OjasKulkarni33/-MED-30.105-Nerf-Gun-Project/Step Files/RotatingDrumSubAssy/Follower.step

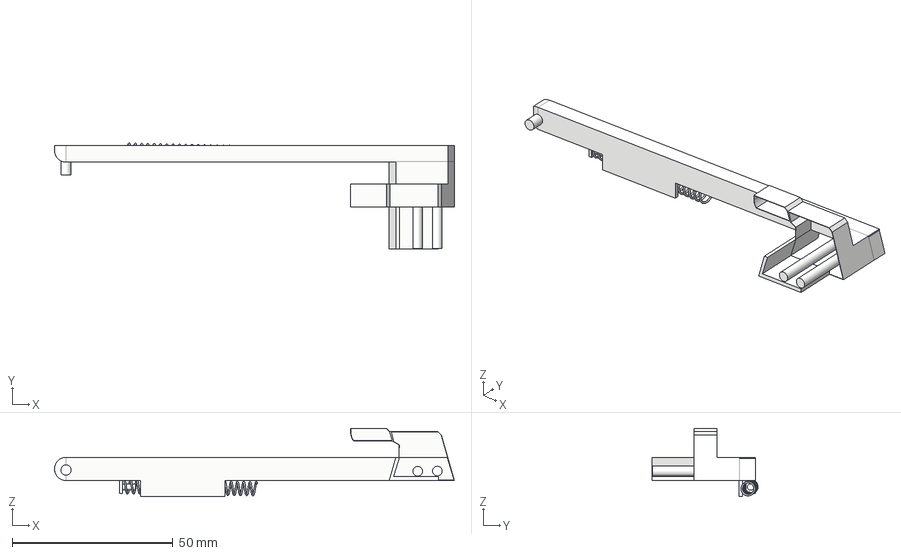
[picture p45: CAD file, 2026-08-20]
Step Files/RotatingDrumSubAssy/Follower.step
124.2 x 33.0 x 21.2 mm
Handle
