OjasKulkarni33/-MED-30.105-Nerf-Gun-Project/Step Files/PrimingSubAssy/Trigger.step

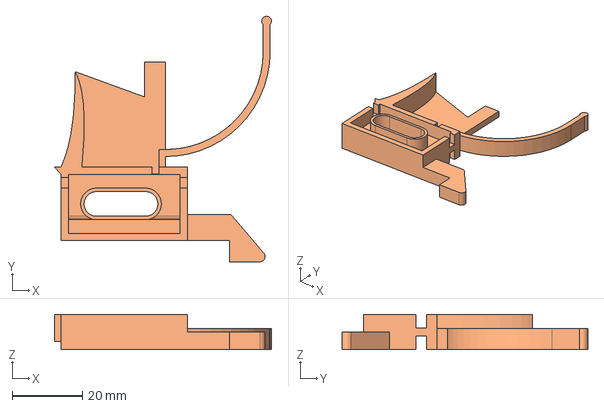
[picture p46: CAD file, 2026-08-20]
Step Files/PrimingSubAssy/Trigger.step
61.9 x 70.0 x 10.0 mm
