OjasKulkarni33/-MED-30.105-Nerf-Gun-Project/Step Files/RotatingDrumSubAssy/ConnectionPiece.step

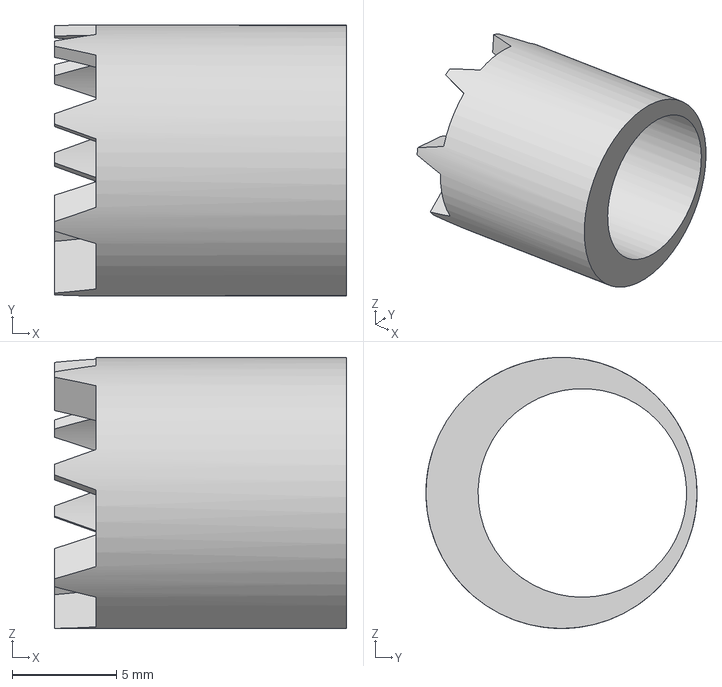
[picture p47: CAD file, 2026-08-20]
Step Files/RotatingDrumSubAssy/ConnectionPiece.step
14.0 x 13.0 x 13.0 mm
