OjasKulkarni33/-MED-30.105-Nerf-Gun-Project/Step Files/CoverFrameSubAssy/CoverFrame_[Right].png

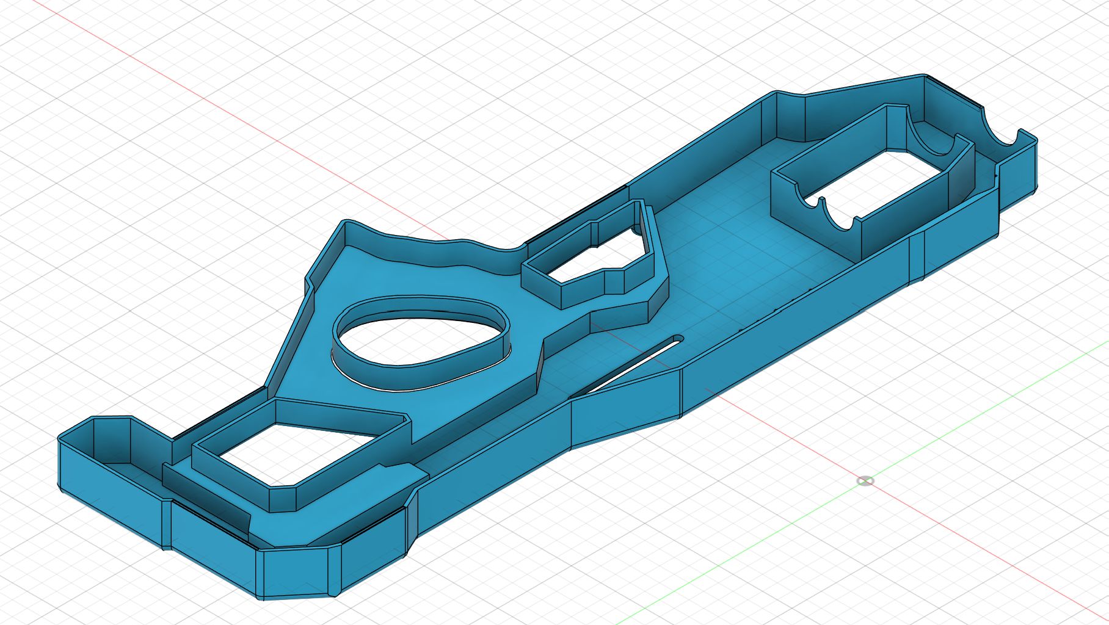
Step Files/CoverFrameSubAssy/CoverFrame_[Right].png
