OjasKulkarni33/-MED-30.105-Nerf-Gun-Project/Step Files/CoverFrameSubAssy/CoverFrameAssembly.png

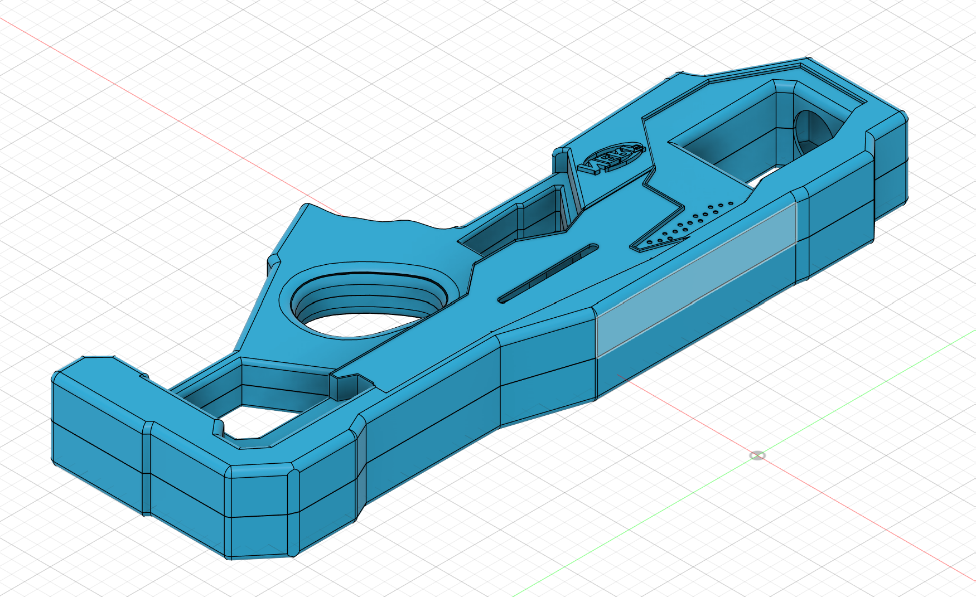
Step Files/CoverFrameSubAssy/CoverFrameAssembly.png
