OjasKulkarni33/-MED-30.105-Nerf-Gun-Project/Step Files/FiringSubAssy/Piston.png

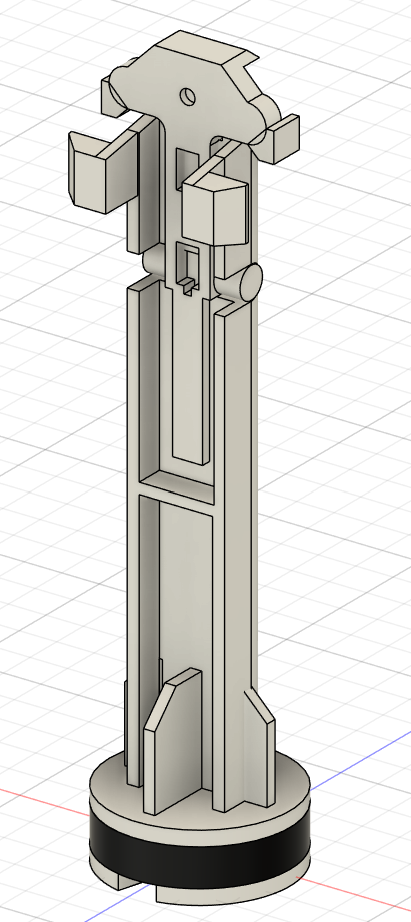
Step Files/FiringSubAssy/Piston.png
