OjasKulkarni33/-MED-30.105-Nerf-Gun-Project/Step Files/FiringSubAssy/PistonHousing.png

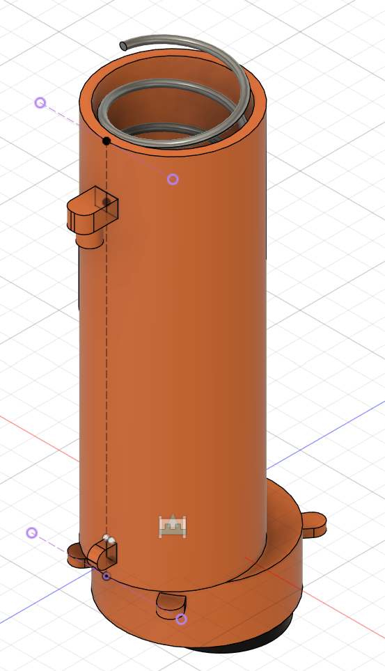
Step Files/FiringSubAssy/PistonHousing.png
