OjasKulkarni33/-MED-30.105-Nerf-Gun-Project/Step Files/InternalFrameSubAssy/InternalFrame[Right].png

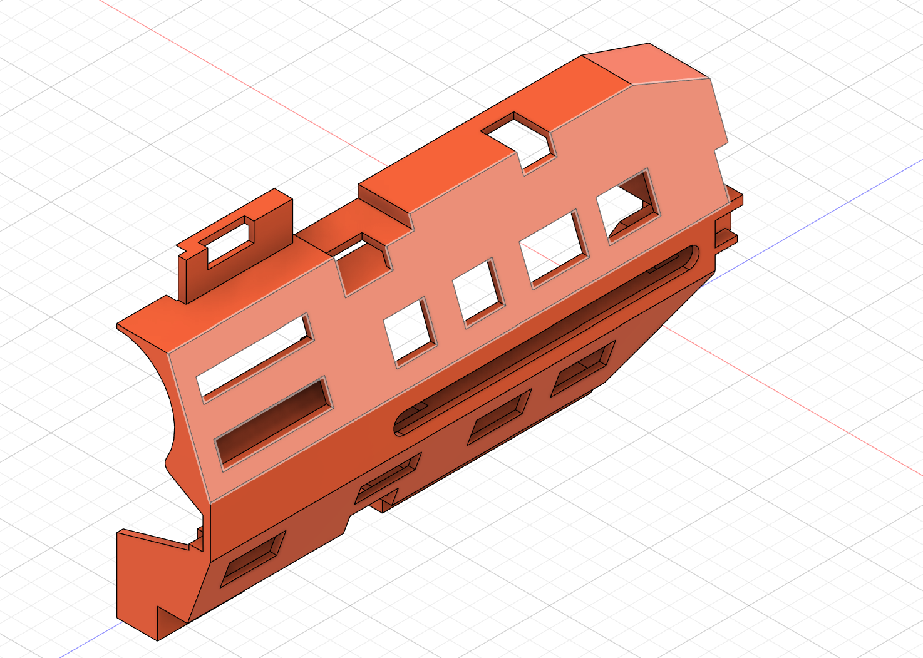
Step Files/InternalFrameSubAssy/InternalFrame[Right].png
