OjasKulkarni33/-MED-30.105-Nerf-Gun-Project/Step Files/InternalFrameSubAssy/InternalrameSubAssy.png

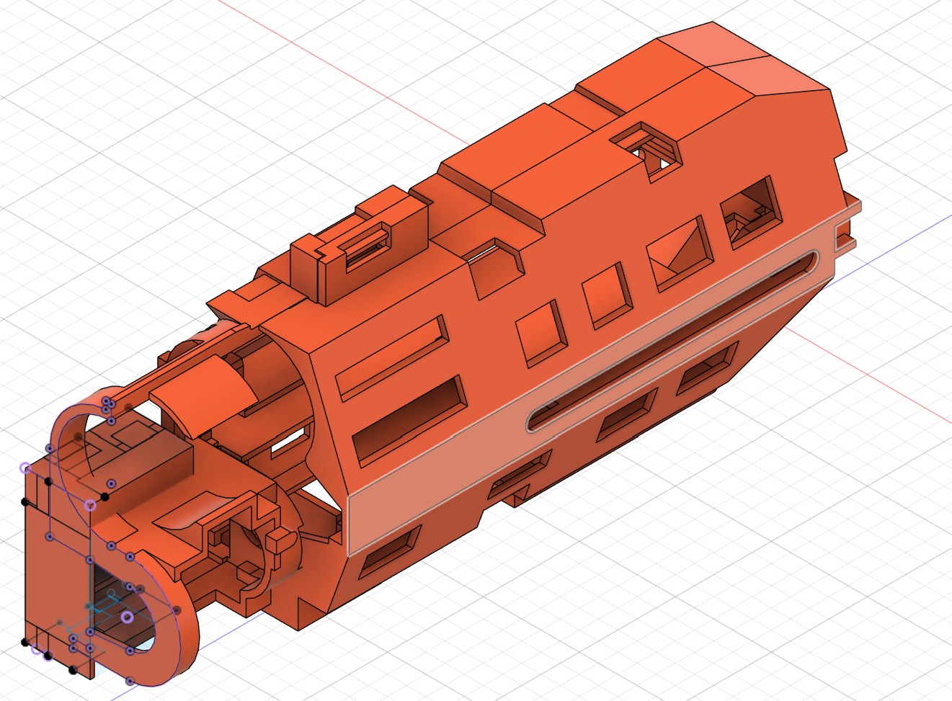
Step Files/InternalFrameSubAssy/InternalrameSubAssy.png
