OjasKulkarni33/-MED-30.105-Nerf-Gun-Project/Step Files/PrimingSubAssy/TriggerLink.png

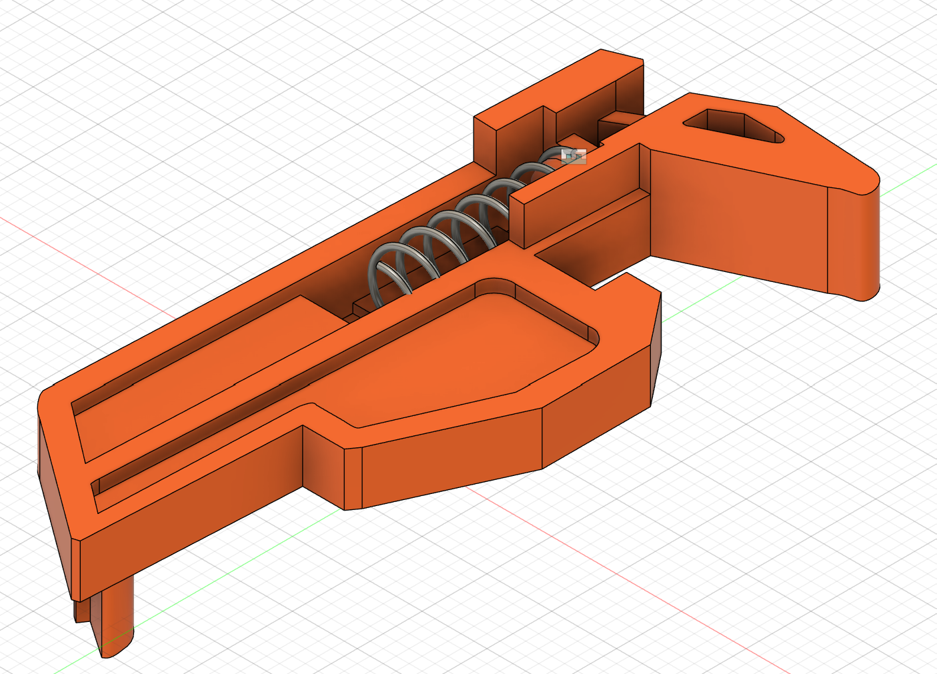
Step Files/PrimingSubAssy/TriggerLink.png
