OjasKulkarni33/-MED-30.105-Nerf-Gun-Project/Step Files/RotatingDrumSubAssy/CAM.png

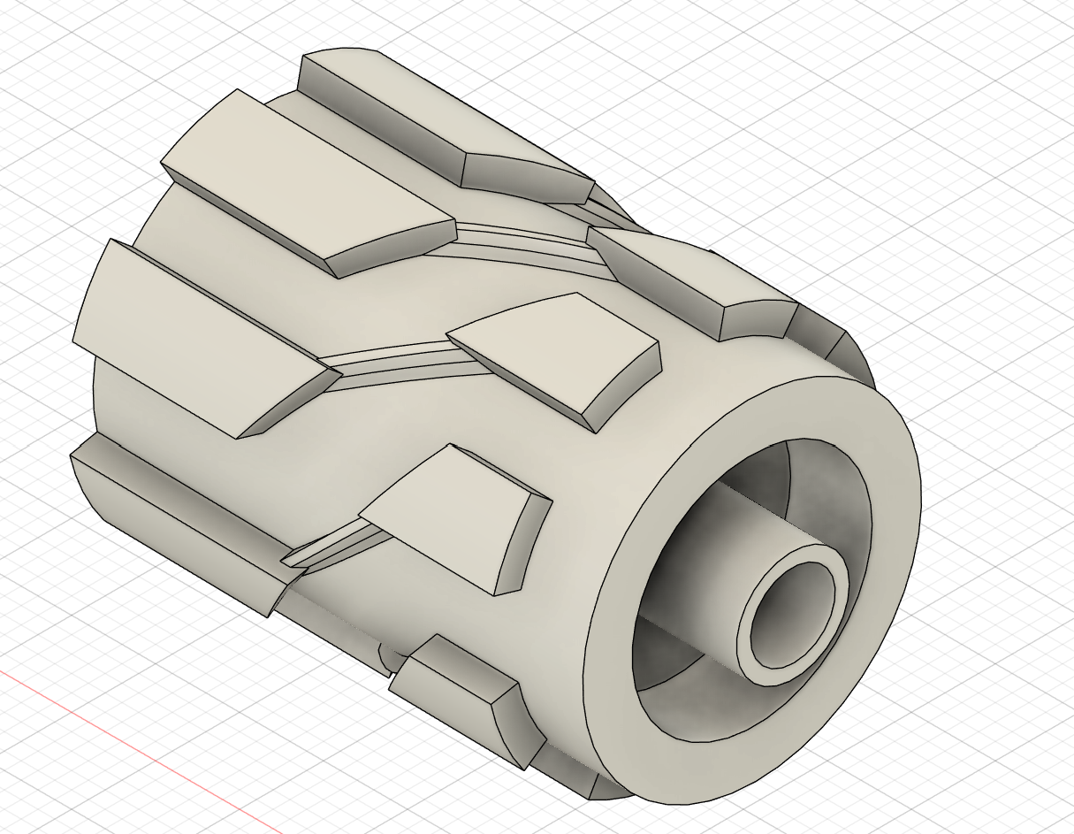
Step Files/RotatingDrumSubAssy/CAM.png
