OjasKulkarni33/-MED-30.105-Nerf-Gun-Project/Step Files/RotatingDrumSubAssy/ConnectionPiece.png

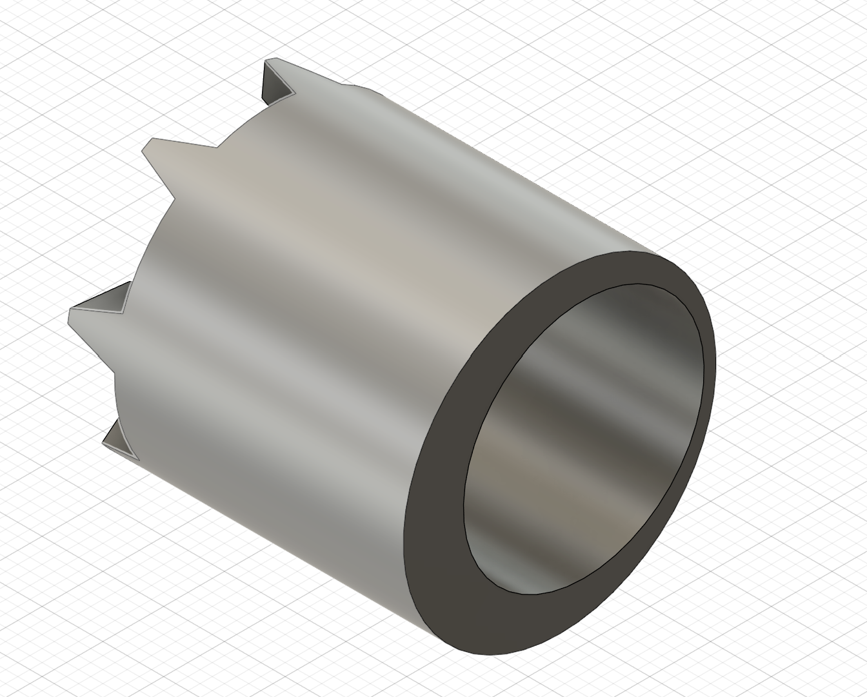
Step Files/RotatingDrumSubAssy/ConnectionPiece.png
