OjasKulkarni33/-MED-30.105-Nerf-Gun-Project/Step Files/RotatingDrumSubAssy/Follower.png

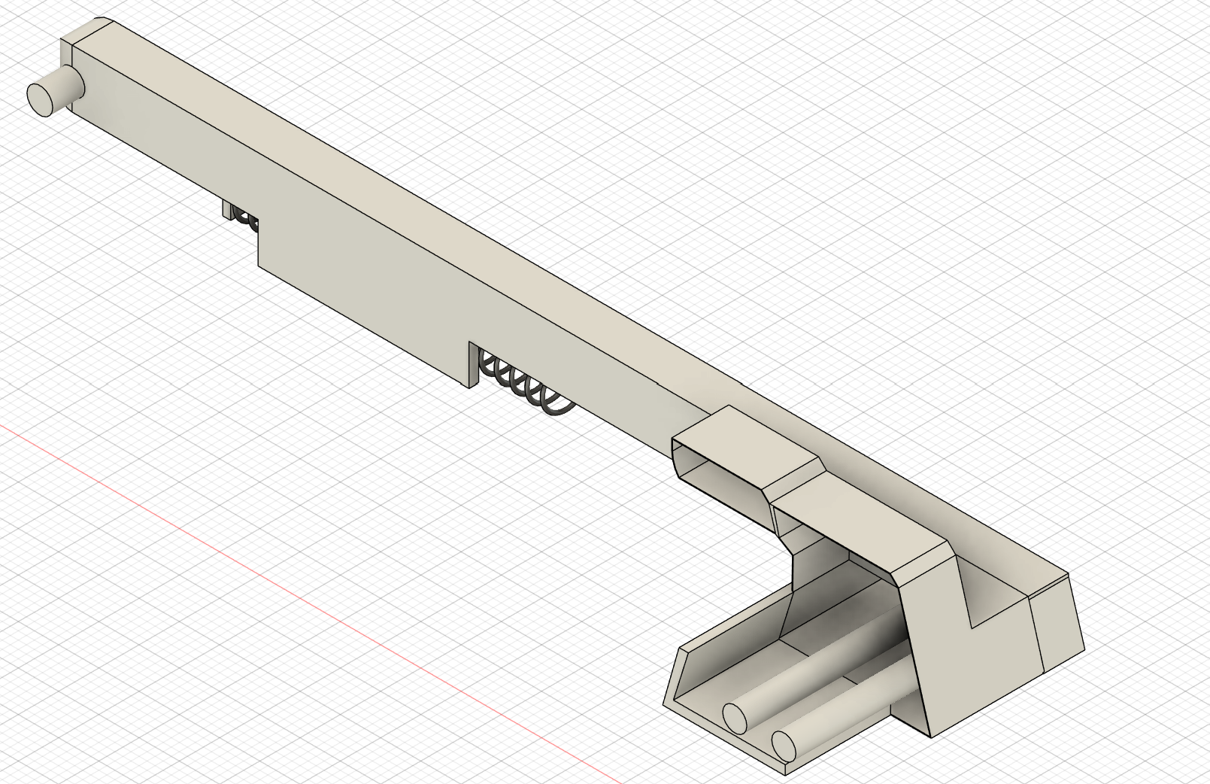
Step Files/RotatingDrumSubAssy/Follower.png
