OjasKulkarni33/-MED-30.105-Nerf-Gun-Project/Step Files/RotatingDrumSubAssy/RotatingDrumSubAssy.png

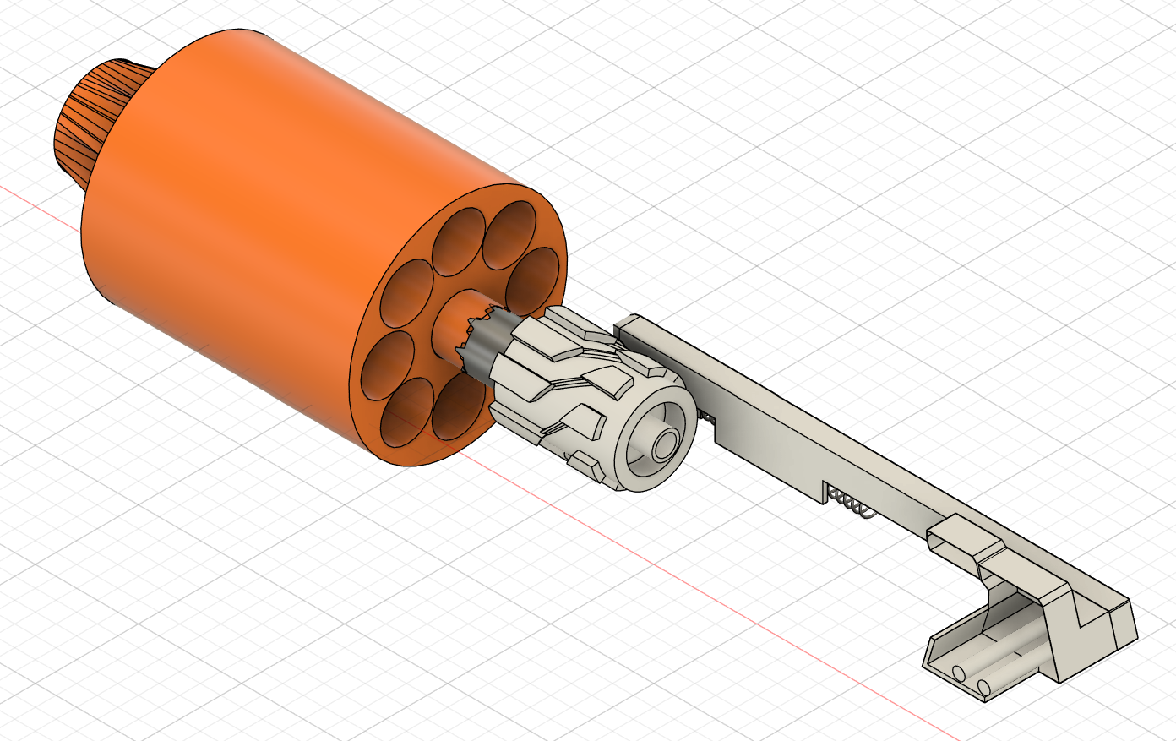
Step Files/RotatingDrumSubAssy/RotatingDrumSubAssy.png
